jackw01/scanlight/data/big scanlight RGB combined.jpg

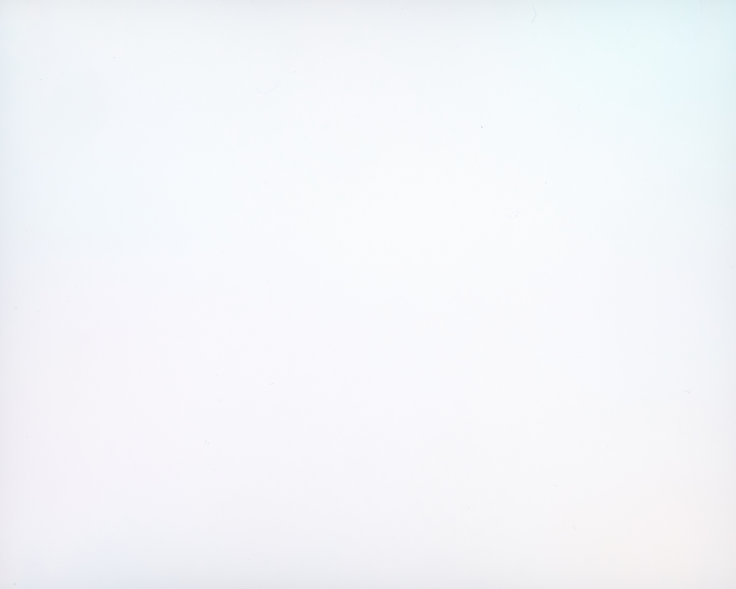
data/big scanlight RGB combined.jpg
