jackw01/scanlight/data/big scanlight white.jpg

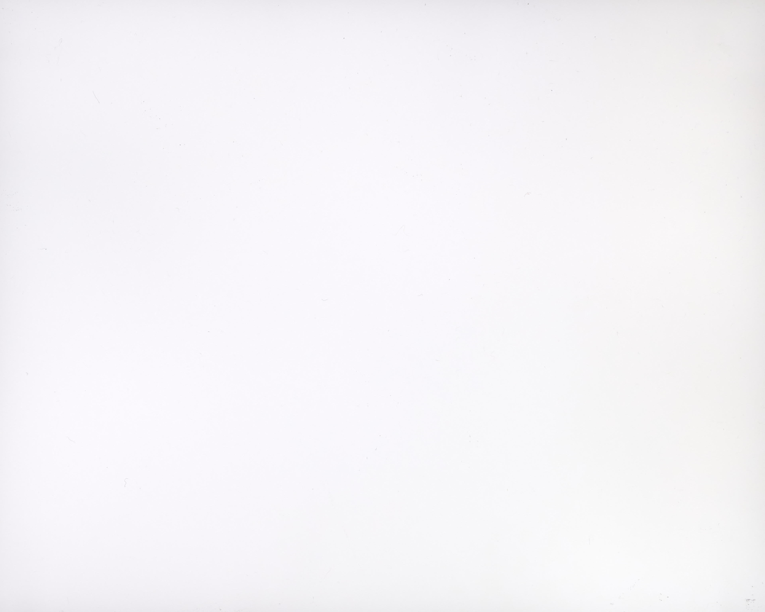
data/big scanlight white.jpg
