jackw01/scanlight/data/center of 15 inch LCD display.png

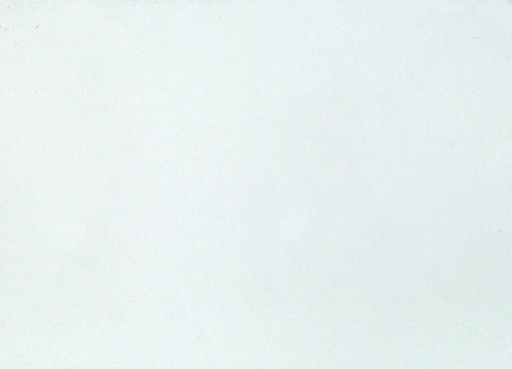
data/center of 15 inch LCD display.png
