jackw01/scanlight/data/competing white LED panel.png

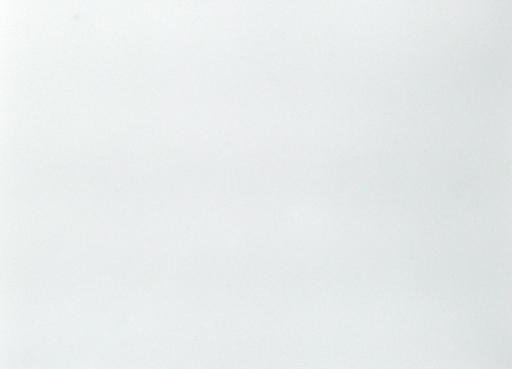
data/competing white LED panel.png
