jackw01/scanlight/data/iPhone 13 Pro.png

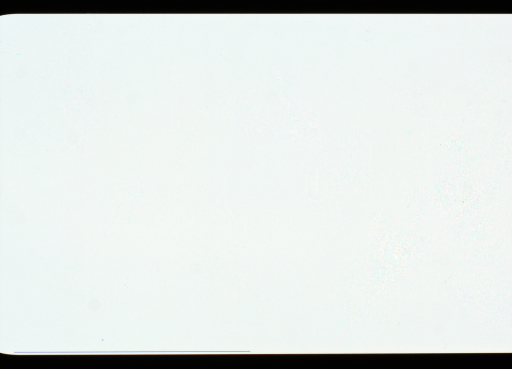
data/iPhone 13 Pro.png
