jackw01/scanlight/data/plots/luminance_plot_iPhone 13 Pro.png

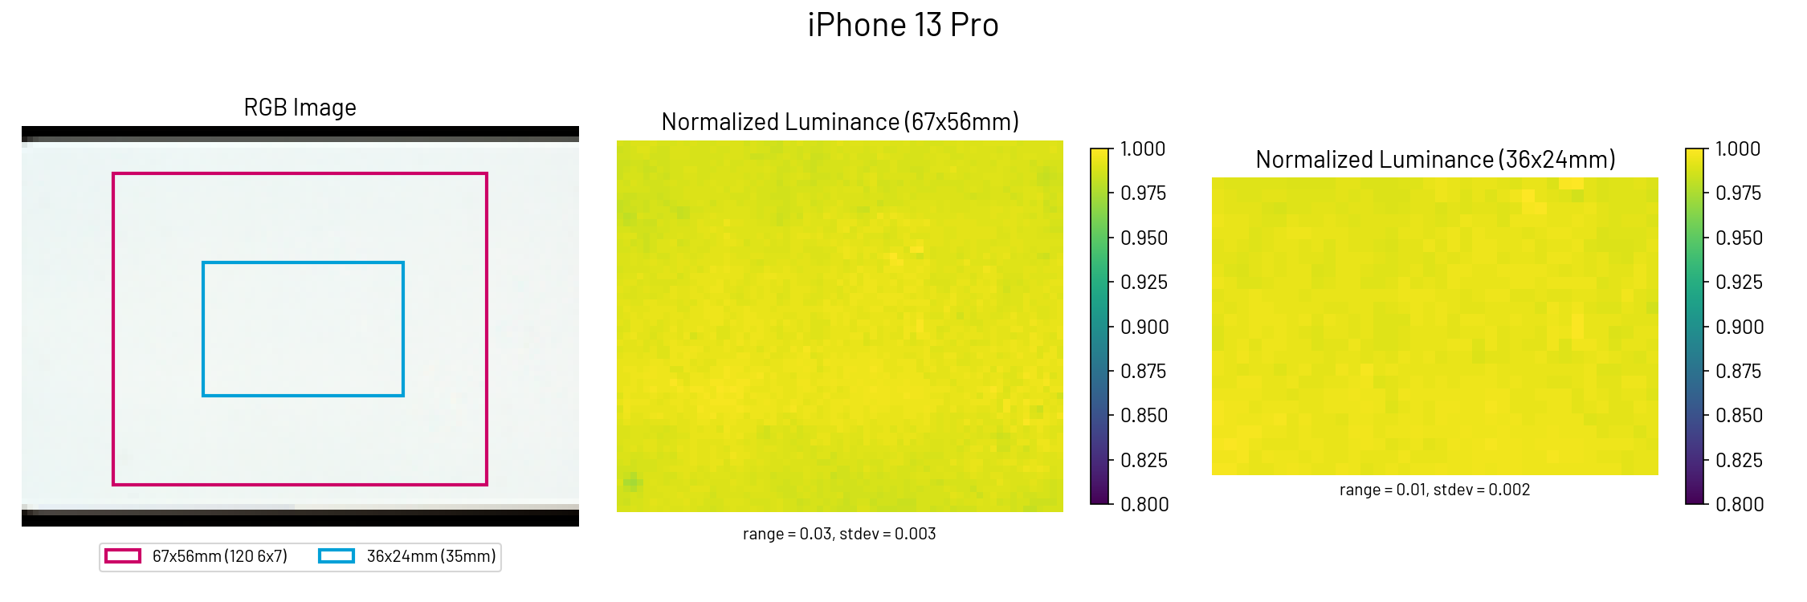
data/plots/luminance_plot_iPhone 13 Pro.png
