jackw01/scanlight/data/scanlight v1.png

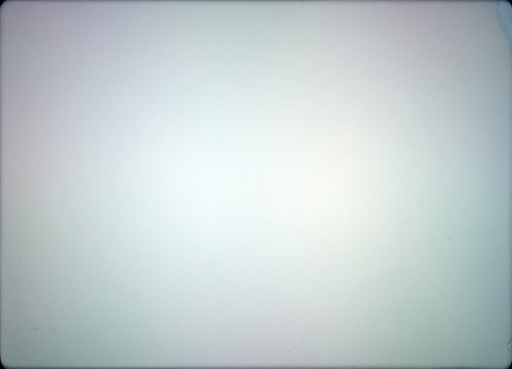
data/scanlight v1.png
