jackw01/scanlight/data/scanlight v4 RGB combined.png

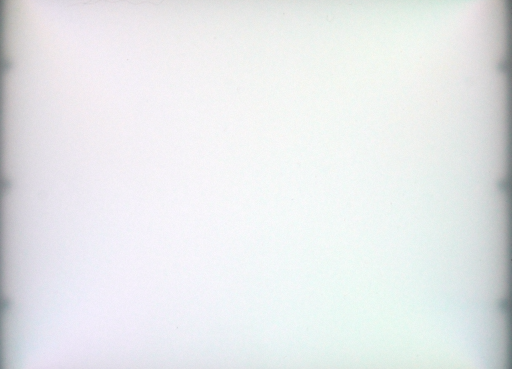
data/scanlight v4 RGB combined.png
