jackw01/scanlight/data/scanlight v4 white.png

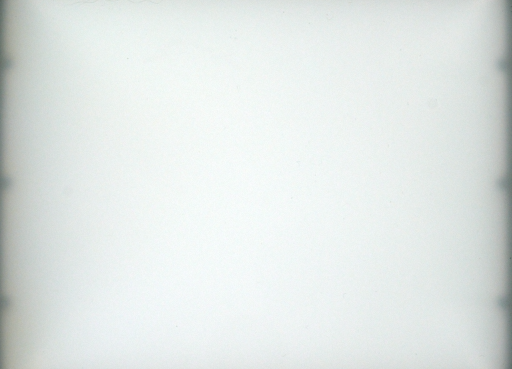
data/scanlight v4 white.png
