jackw01/scanlight/images/ac_adapter.jpg

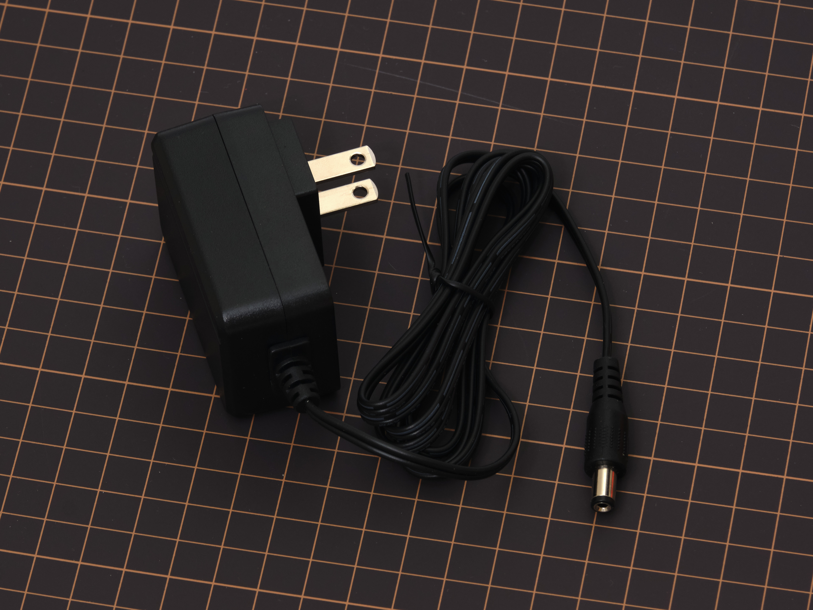
images/ac_adapter.jpg
