jackw01/scanlight/images/app.png

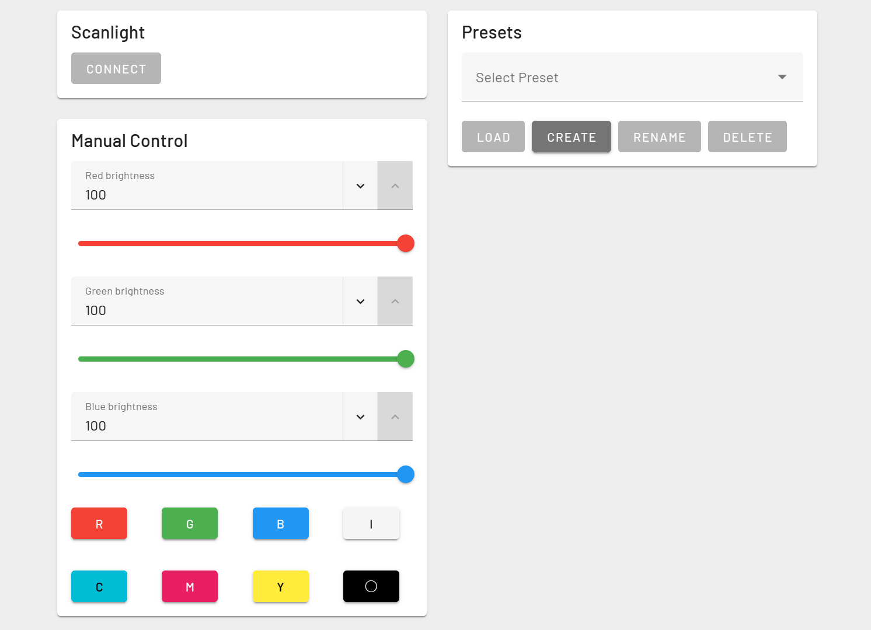
images/app.png
