jackw01/scanlight/images/big_scanlight_lit_2.jpg

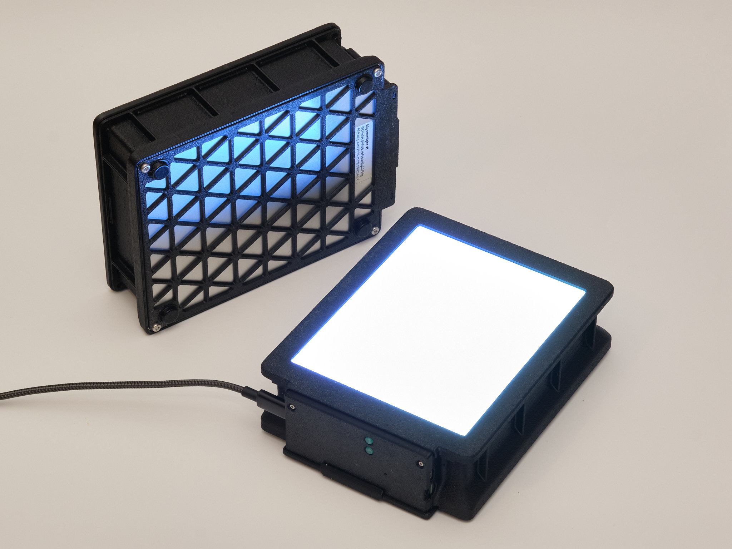
images/big_scanlight_lit_2.jpg
