jackw01/scanlight/images/big_scanlight_lit_3.jpg

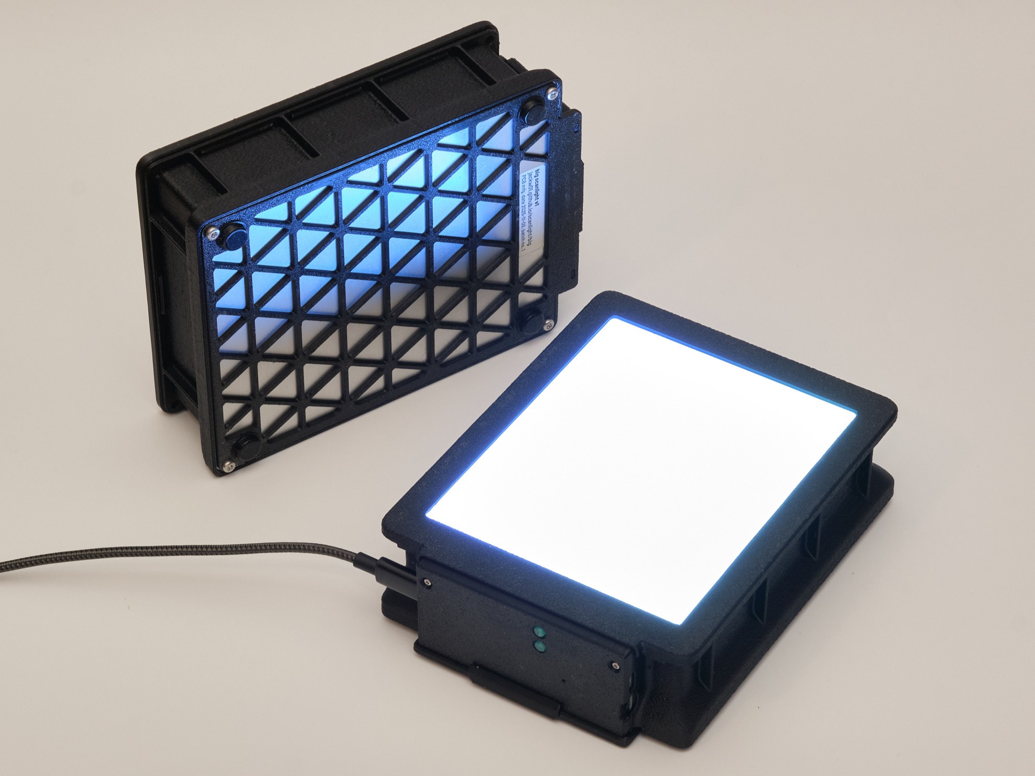
images/big_scanlight_lit_3.jpg
