jackw01/scanlight/images/big_scanlight_top.jpg

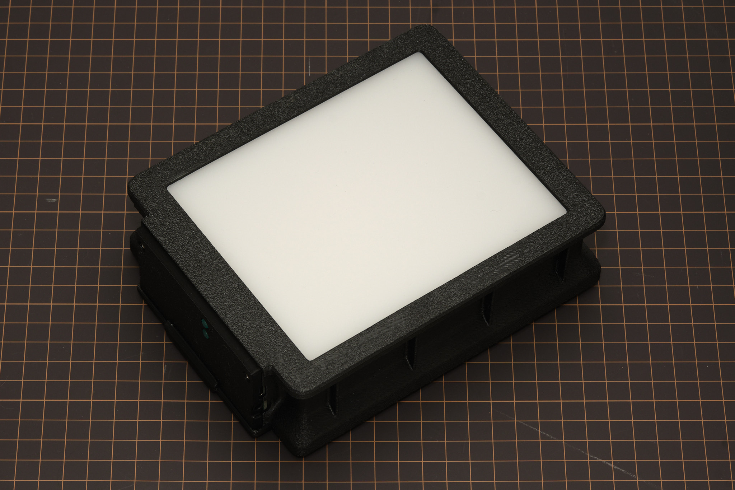
images/big_scanlight_top.jpg
