jackw01/scanlight/images/comparison3.jpg

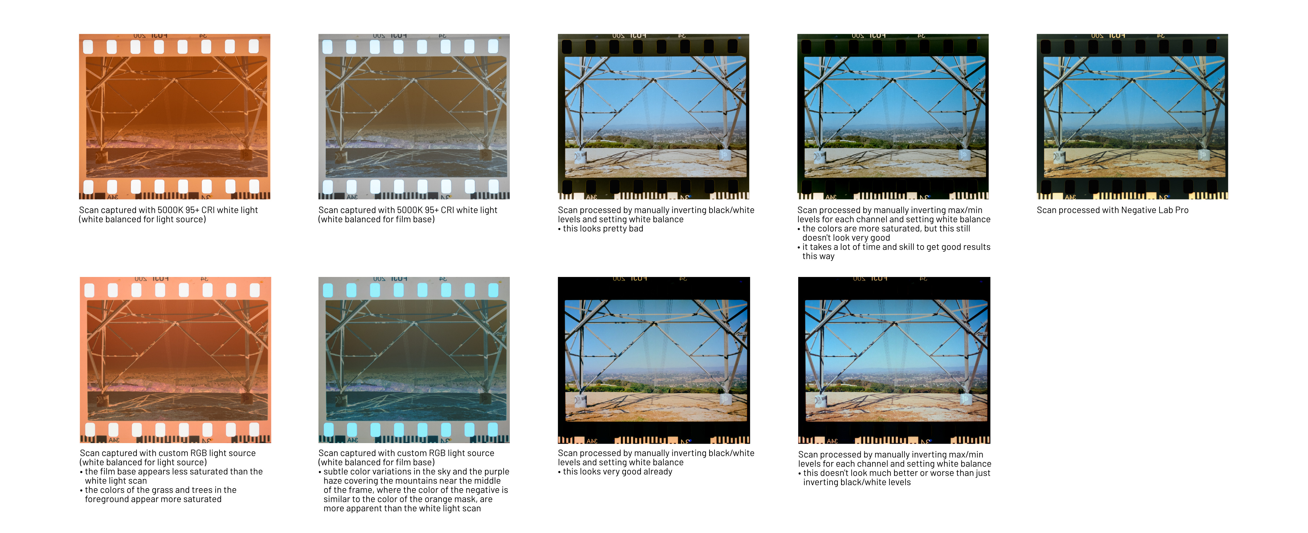
images/comparison3.jpg
