jackw01/scanlight/images/comparison.jpg

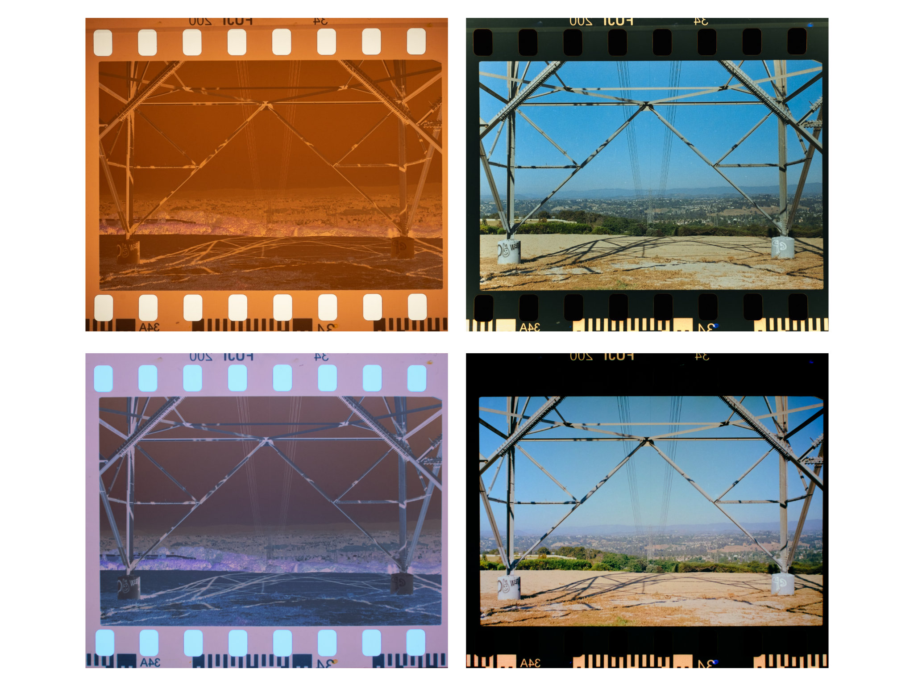
images/comparison.jpg
