jackw01/scanlight/images/diffuser_stackup.png

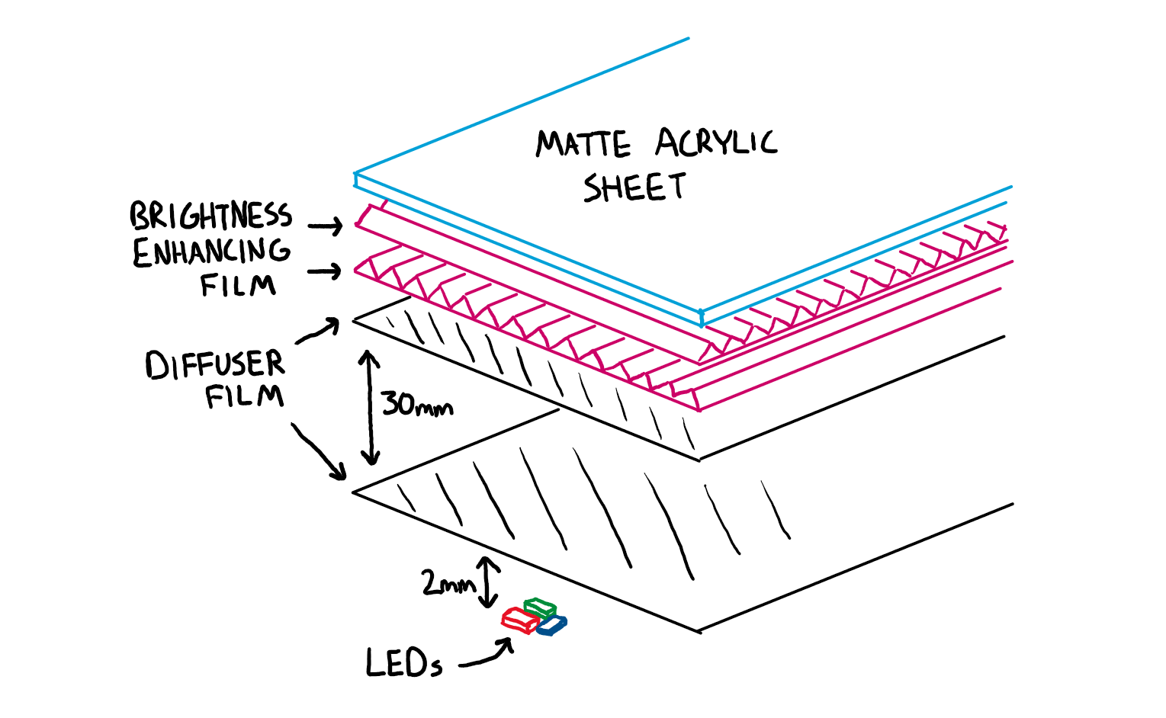
images/diffuser_stackup.png
