jackw01/scanlight/images/film_carrier_adapter.jpg

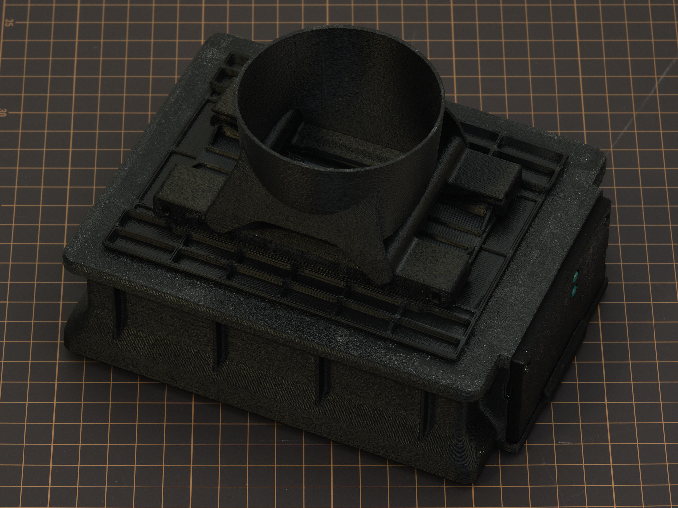
images/film_carrier_adapter.jpg
