jackw01/scanlight/images/filmcarriers_back_2.jpg

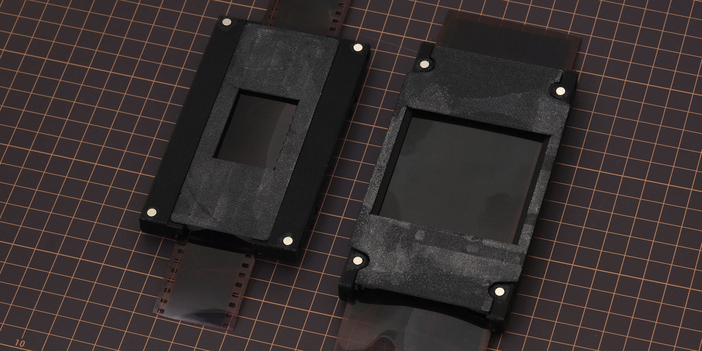
images/filmcarriers_back_2.jpg
