jackw01/scanlight/images/filmcarriers_front_2.jpg

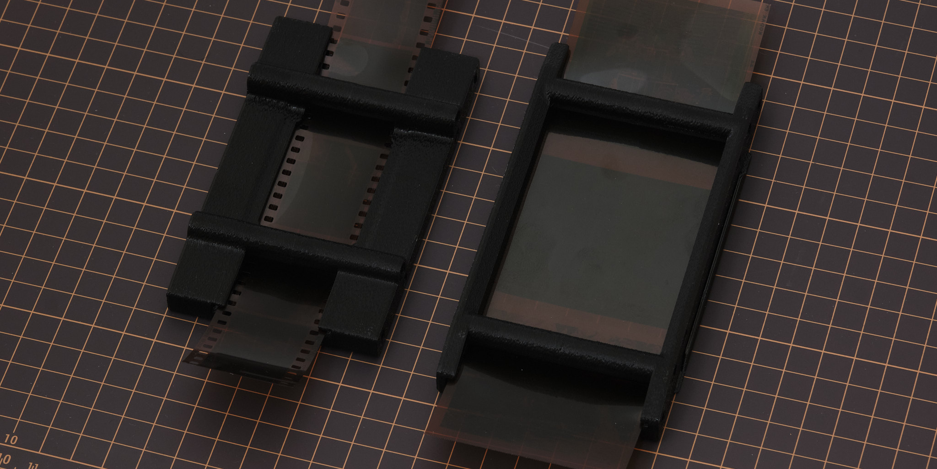
images/filmcarriers_front_2.jpg
