jackw01/scanlight/images/light_with_film_v2_2.jpg

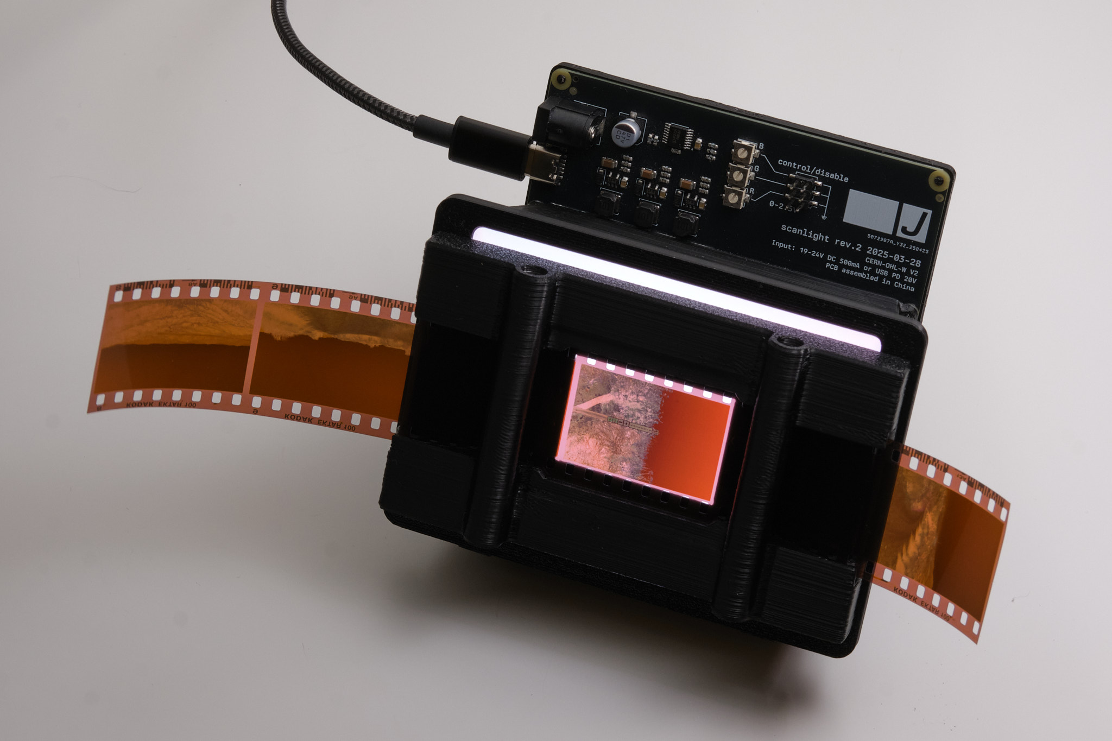
images/light_with_film_v2_2.jpg
