jackw01/scanlight/images/pcb.jpg

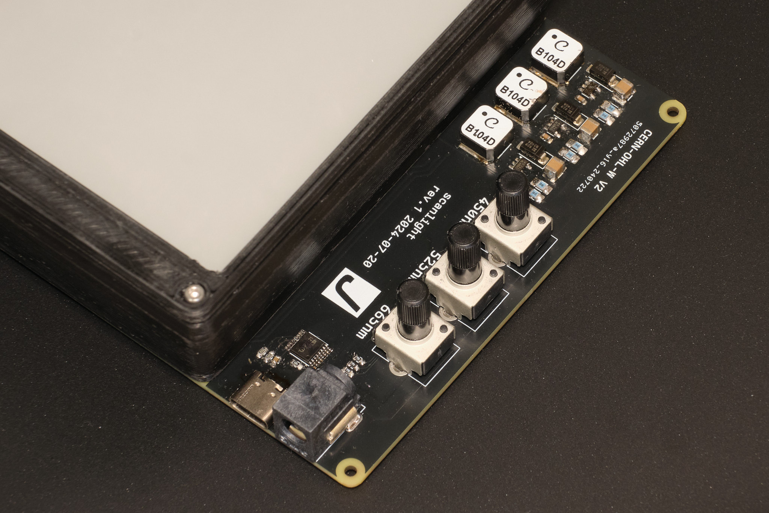
images/pcb.jpg
