jackw01/scanlight/images/pcb_cad.png

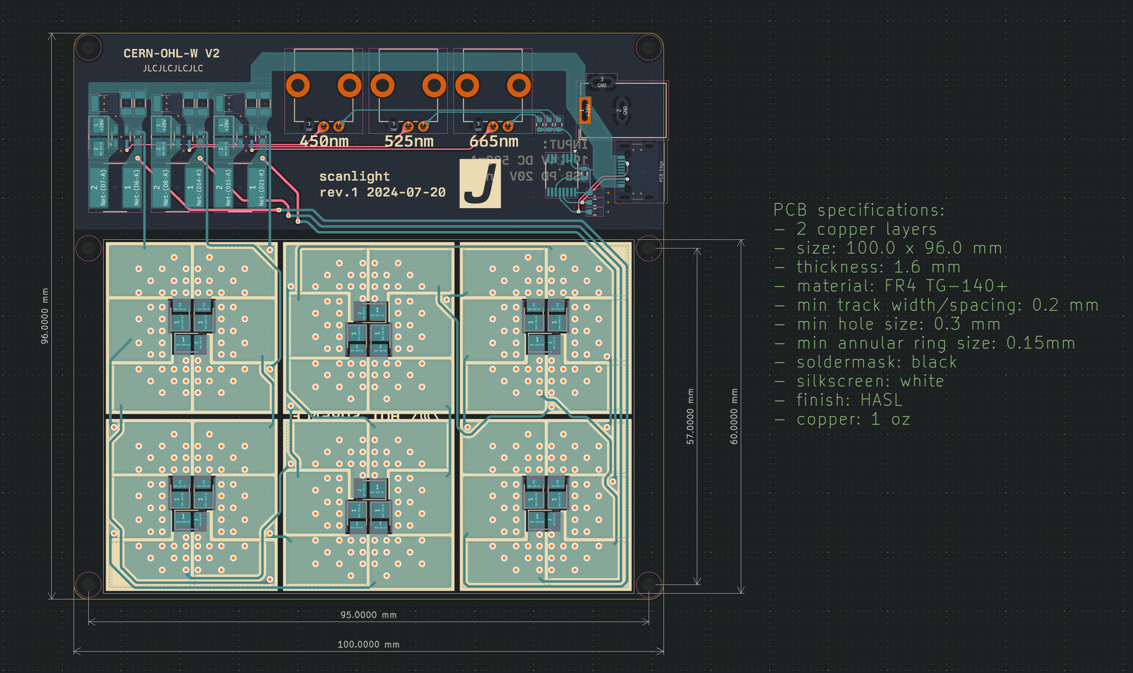
images/pcb_cad.png
