jackw01/scanlight/images/pcb_cad_r2.png

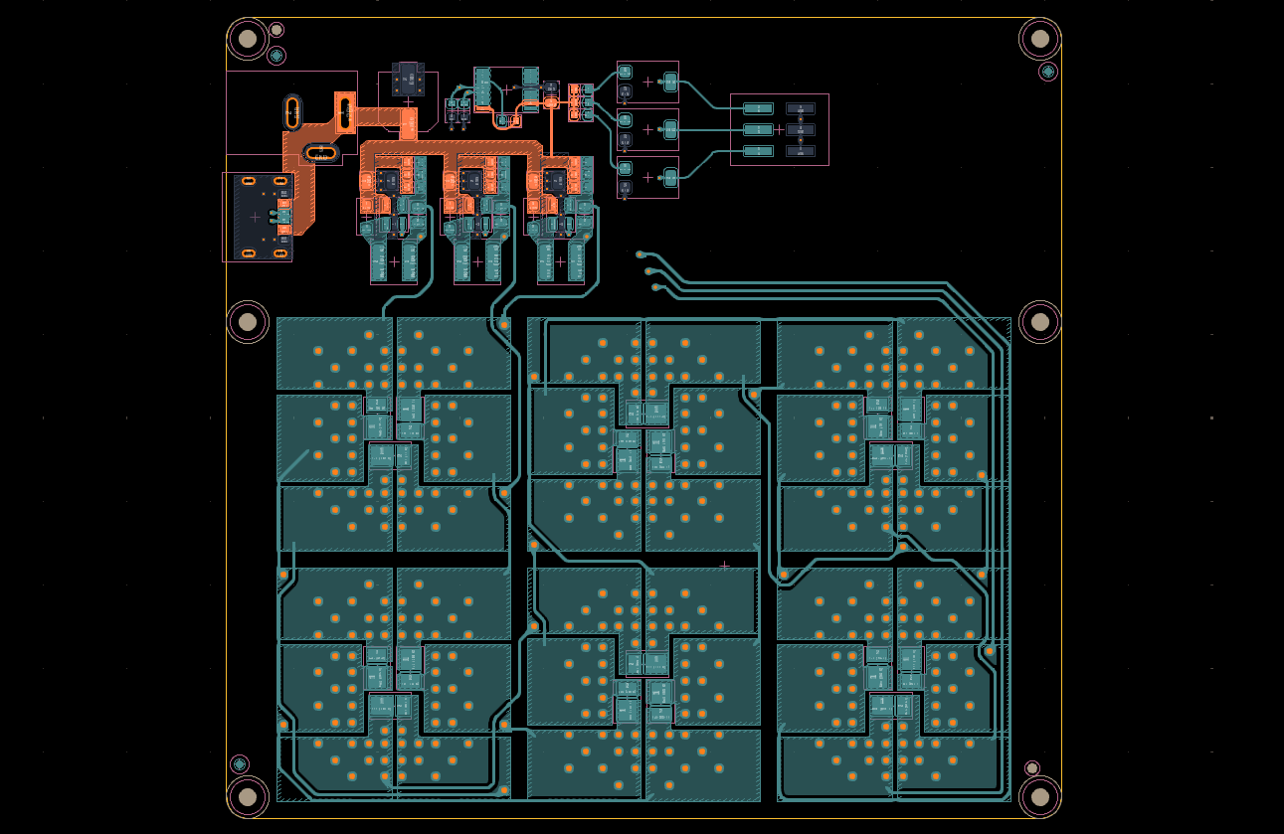
images/pcb_cad_r2.png
