jackw01/scanlight/images/pcb_r2.png

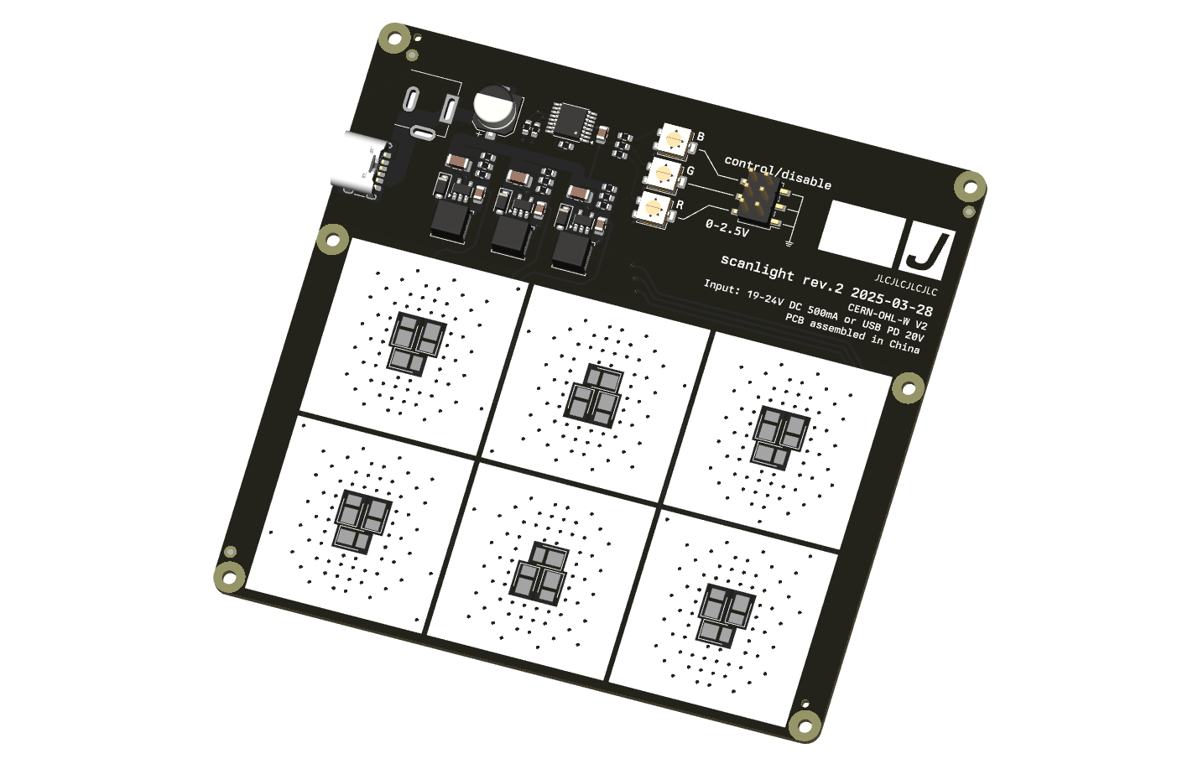
images/pcb_r2.png
