jackw01/scanlight/images/scan_comparison_aerocolor_1.jpg

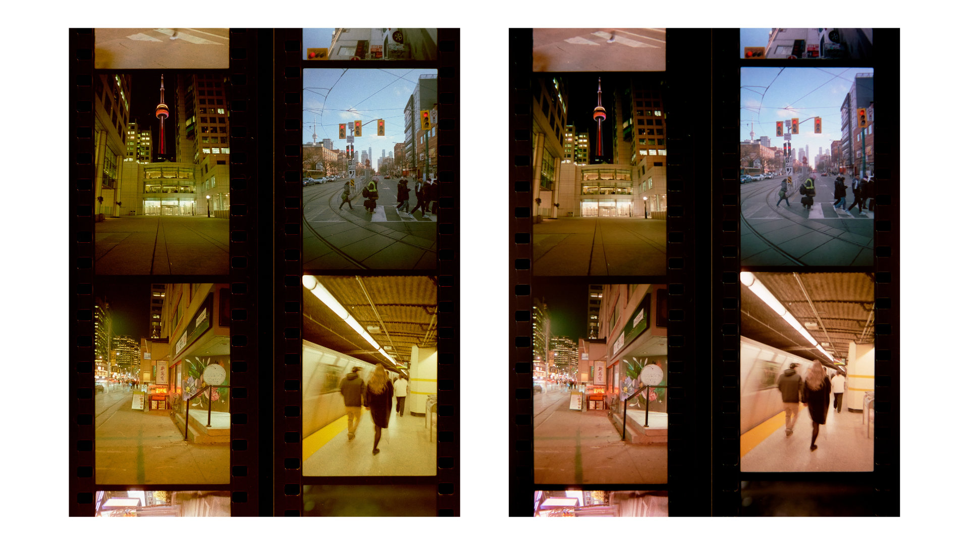
images/scan_comparison_aerocolor_1.jpg
