jackw01/scanlight/images/scan_comparison_ektar_3.jpg

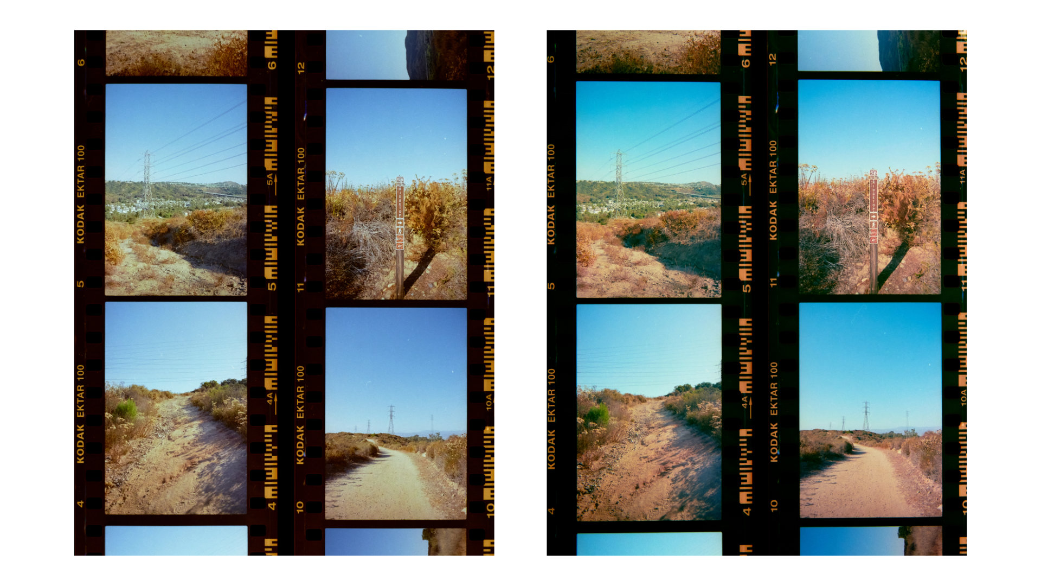
images/scan_comparison_ektar_3.jpg
