jackw01/scanlight/images/scan_comparison_fuji200_1.jpg

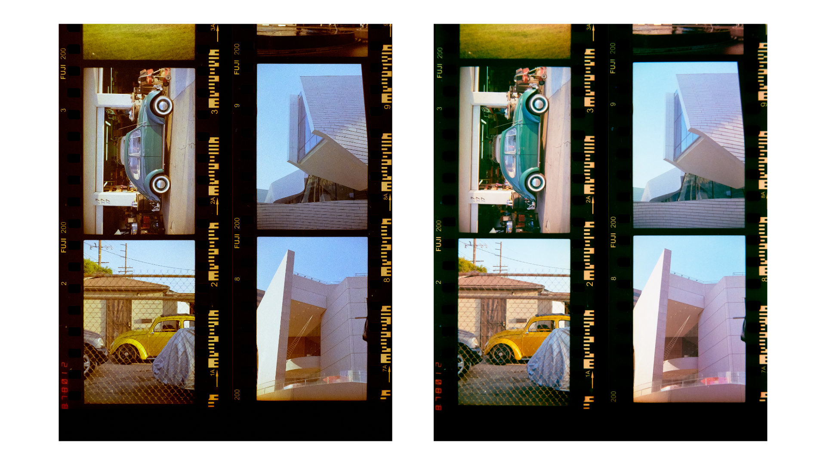
images/scan_comparison_fuji200_1.jpg
