jackw01/scanlight/images/scan_comparison_fuji200_2.jpg

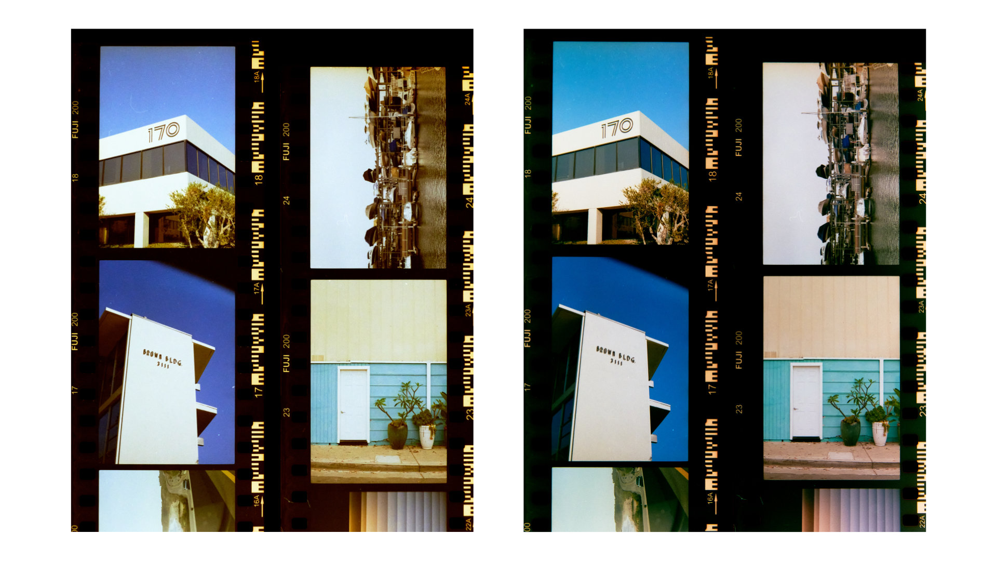
images/scan_comparison_fuji200_2.jpg
