jackw01/scanlight/images/scanlight_v2_back.jpg

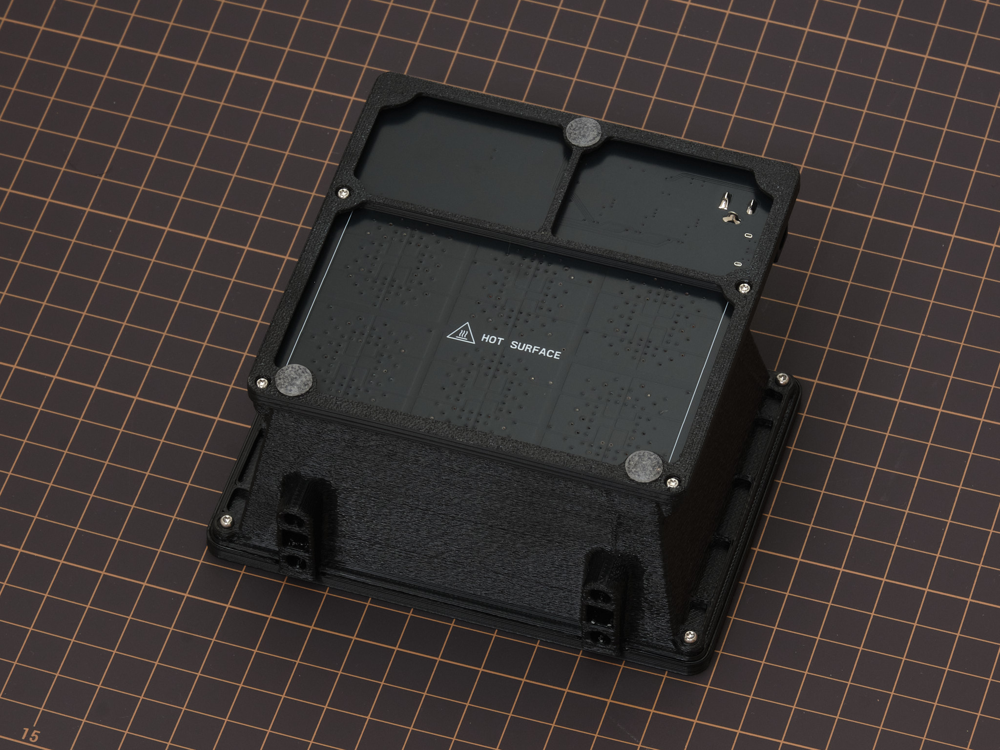
images/scanlight_v2_back.jpg
