jackw01/scanlight/images/scanlight_v2_cad.png

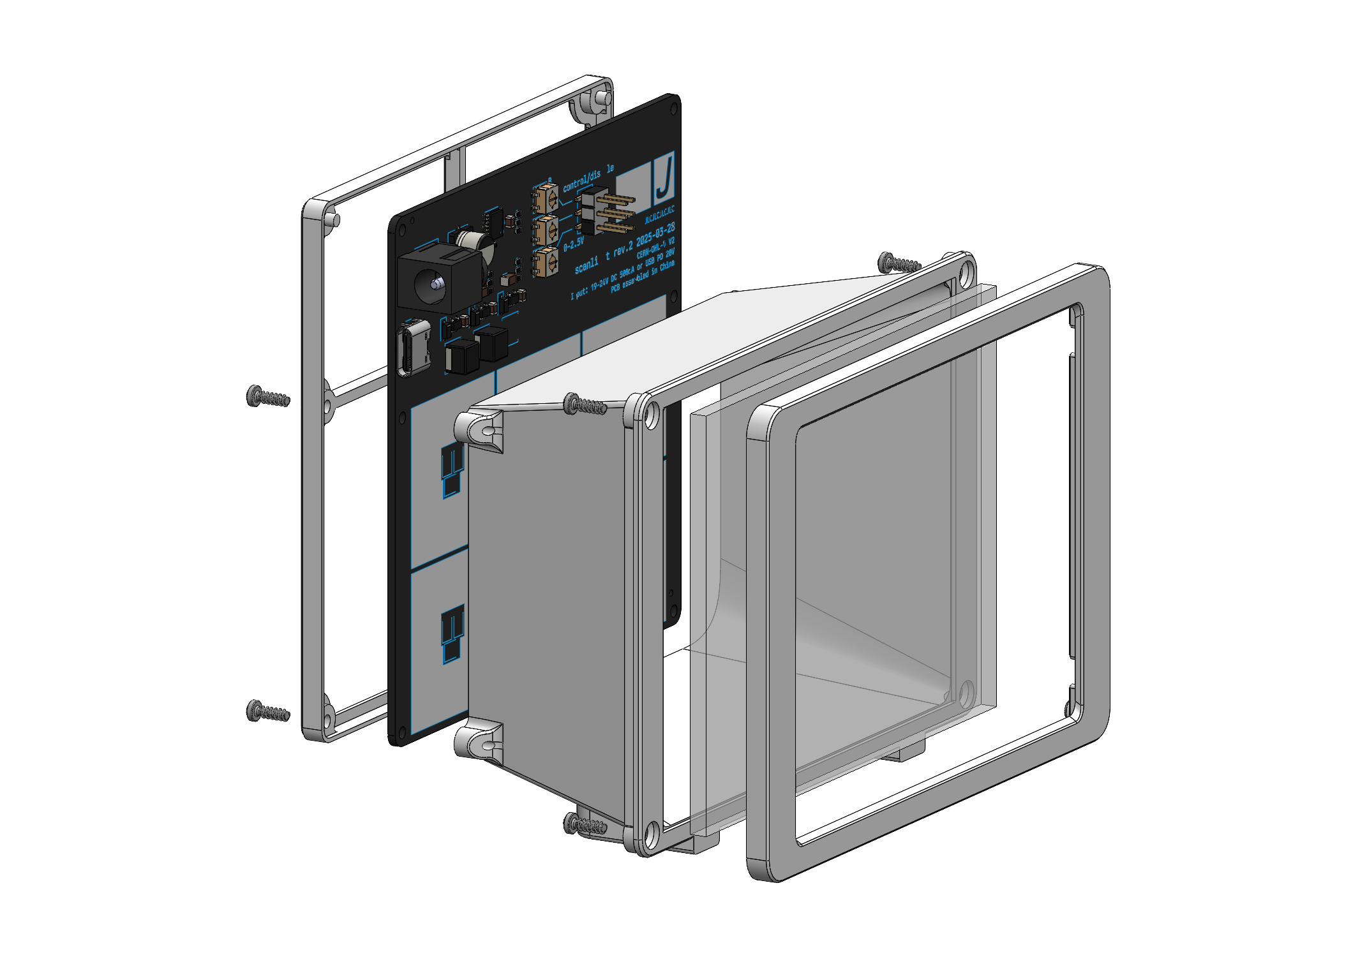
images/scanlight_v2_cad.png
