jackw01/scanlight/images/scanlight_v4_bottom.jpg

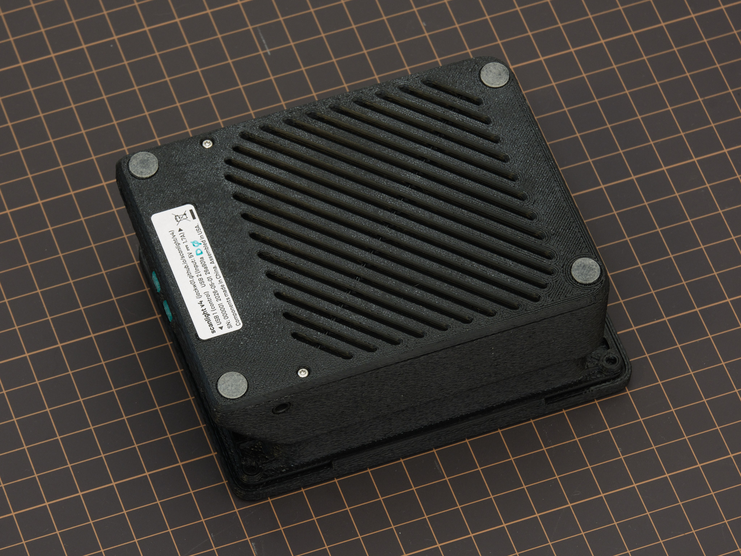
images/scanlight_v4_bottom.jpg
