jackw01/scanlight/images/scanlight_v4_dimension_drawing.png

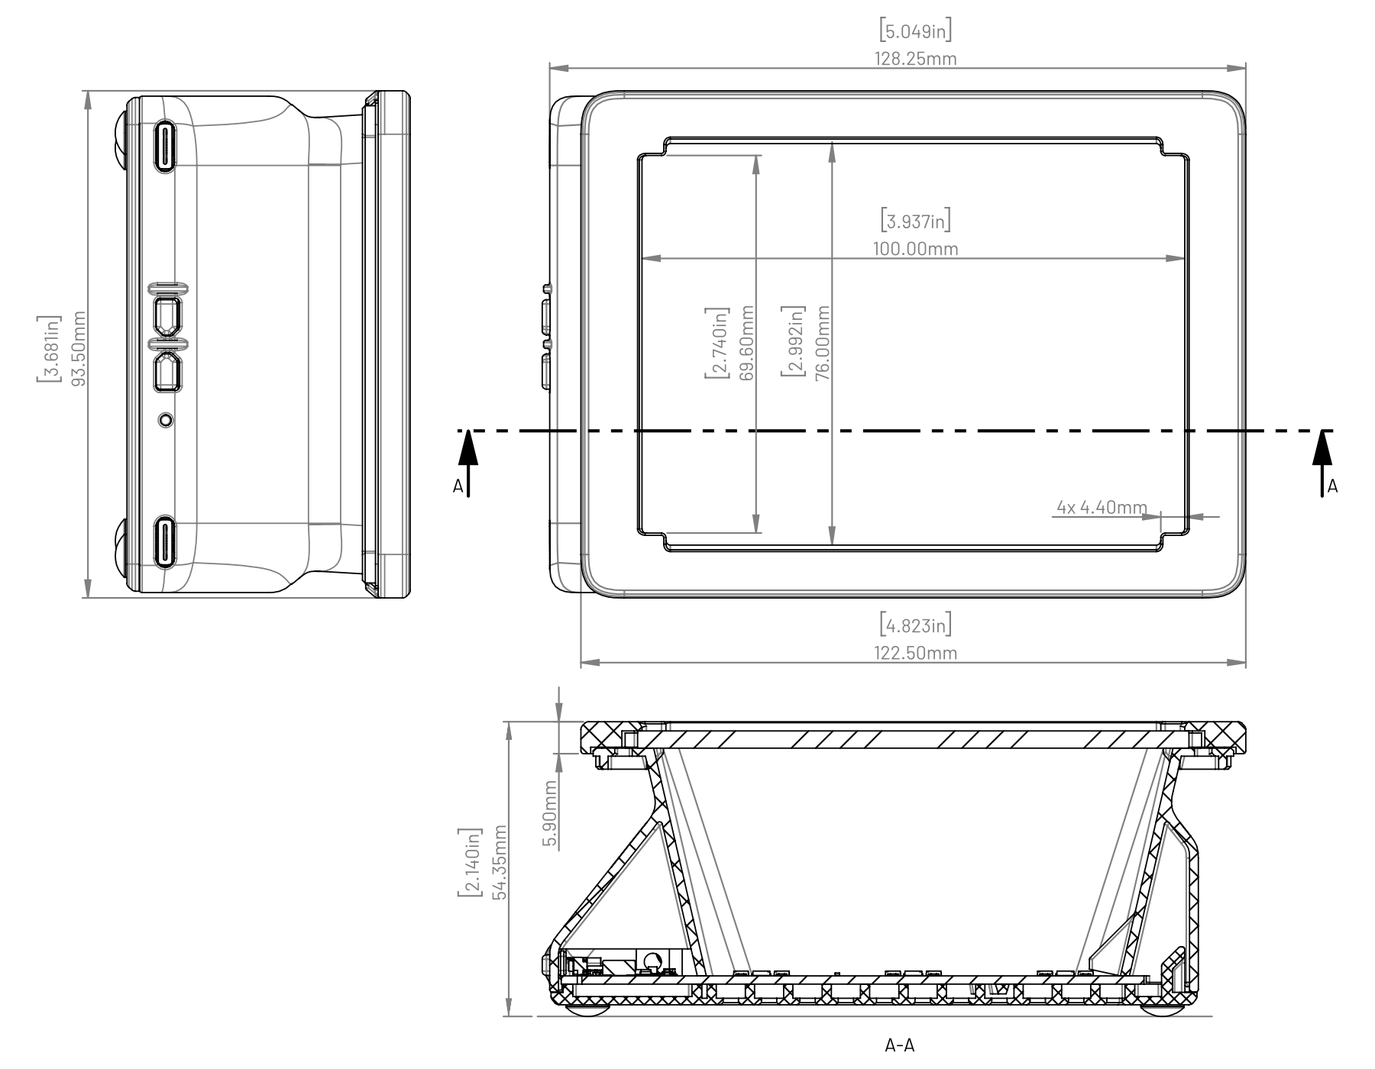
images/scanlight_v4_dimension_drawing.png
