jackw01/scanlight/images/scanlight_v4_lit_2.jpg

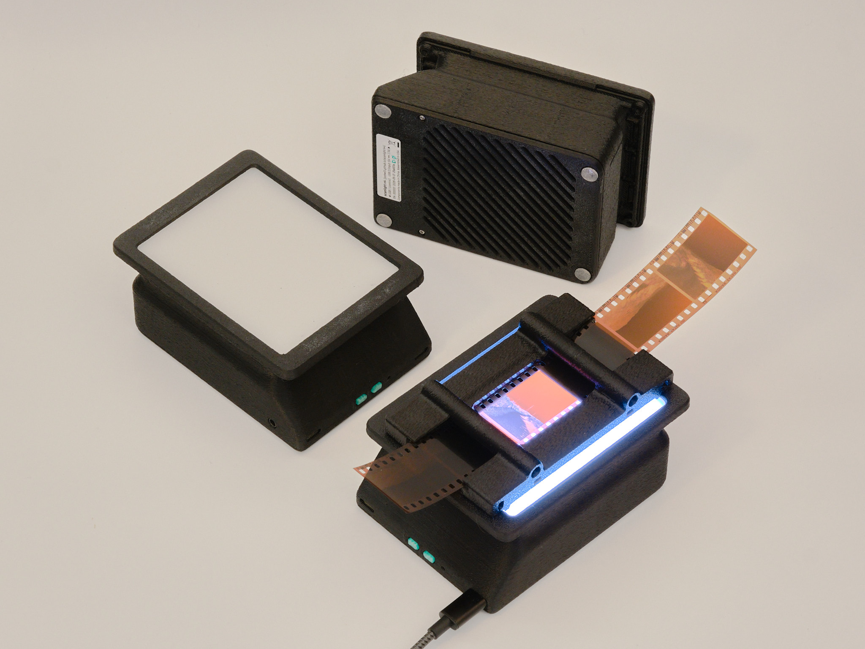
images/scanlight_v4_lit_2.jpg
