jackw01/scanlight/images/webapp.png

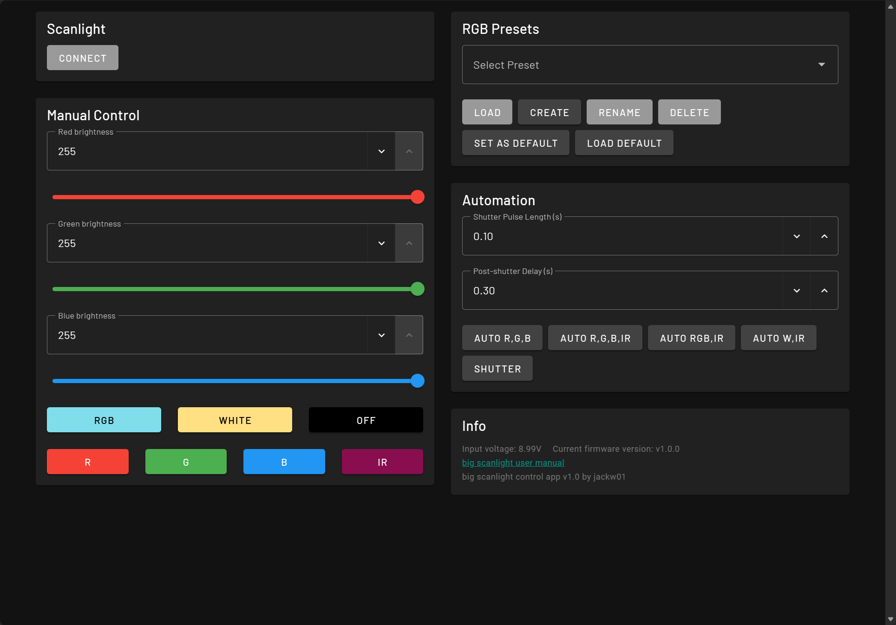
images/webapp.png
