jackw01/scanlight/3d/scanlight v4/26a110b tonecarrier compatibility plate.step

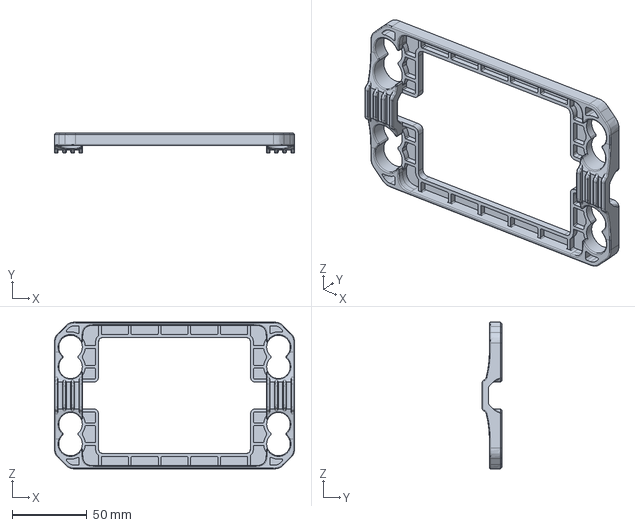
[picture p106: CAD file, 2026-06-06]
3d/scanlight v4/26a110b tonecarrier compatibility plate.step
161.0 x 13.5 x 98.4 mm
