jackw01/scanlight/3d/big scanlight v1/25d107 button.step

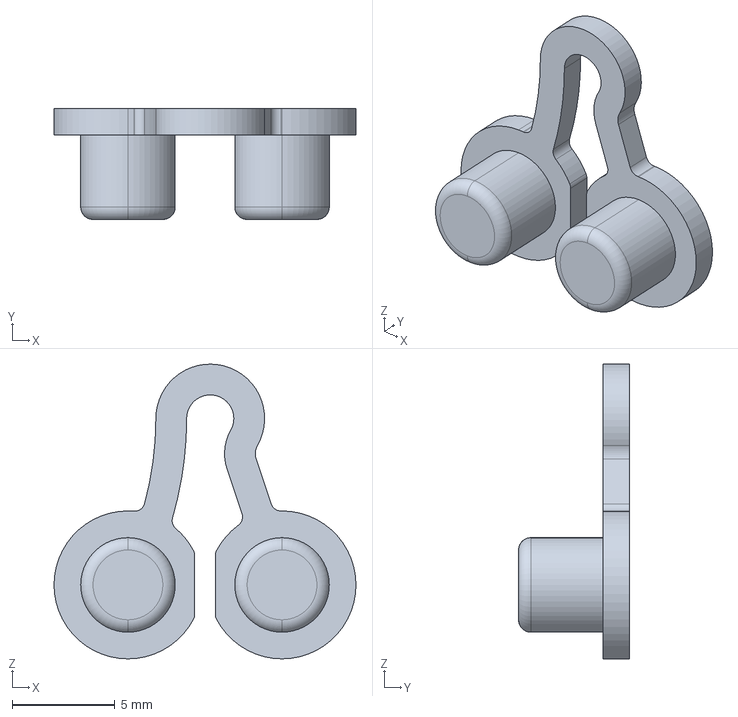
[picture p107: CAD file, 2026-09-24]
3d/big scanlight v1/25d107 button.step
14.7 x 5.40 x 14.3 mm
