jackw01/scanlight/3d/film carriers v1.1/25c014 120 68 mask.step

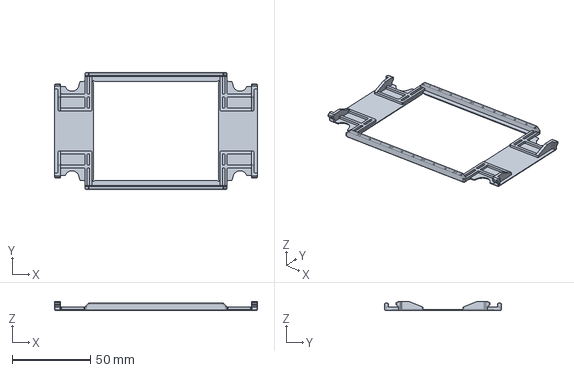
[picture p108: CAD file, 2026-05-09]
3d/film carriers v1.1/25c014 120 68 mask.step
130.0 x 75.0 x 5.80 mm
