jackw01/scanlight/3d/horizontal/25c036 camera clamp cam.step

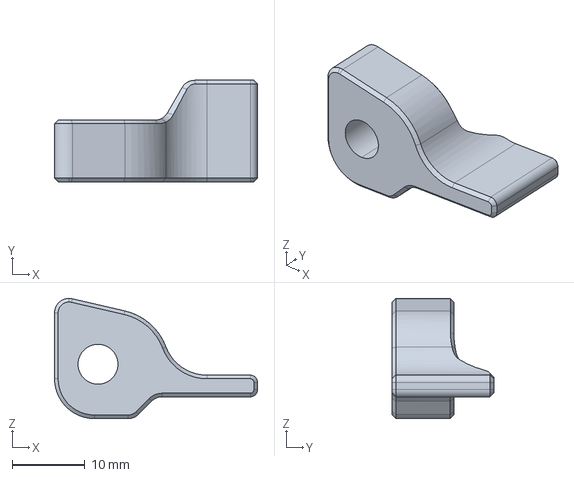
[picture p109: CAD file, 2025-08-15]
3d/horizontal/25c036 camera clamp cam.step
28.0 x 14.0 x 16.6 mm
