jackw01/scanlight/3d/light source v3/25c-p003b diffuser bezel.step

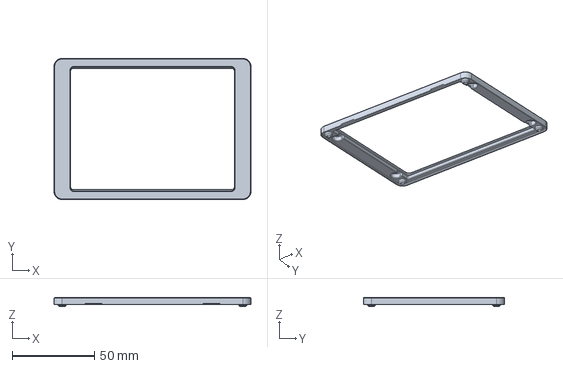
[picture p110: CAD file, 2025-08-02]
3d/light source v3/25c-p003b diffuser bezel.step
120.0 x 86.0 x 5.60 mm
