jackw01/scanlight/3d/scanlight v4/26a005 pcb cover.step

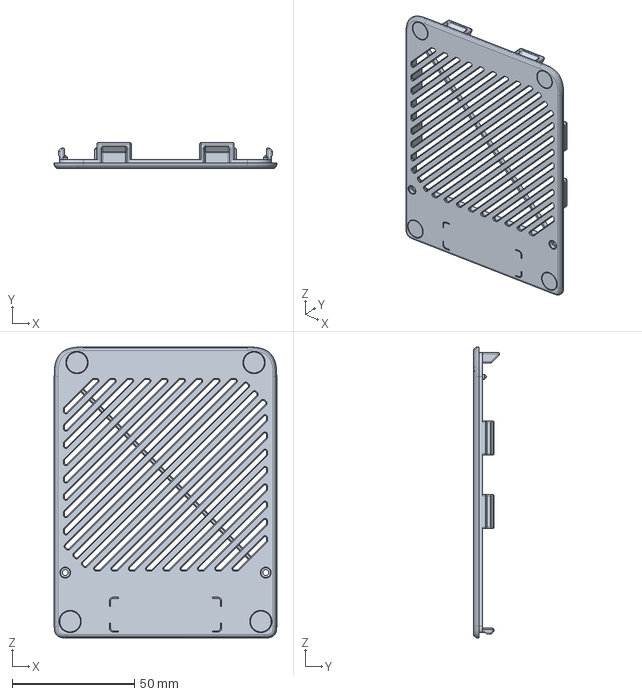
[picture p111: CAD file, 2026-05-09]
3d/scanlight v4/26a005 pcb cover.step
91.0 x 10.7 x 119.0 mm
