jackw01/scanlight/3d/big scanlight v1/25d104 backplate.step

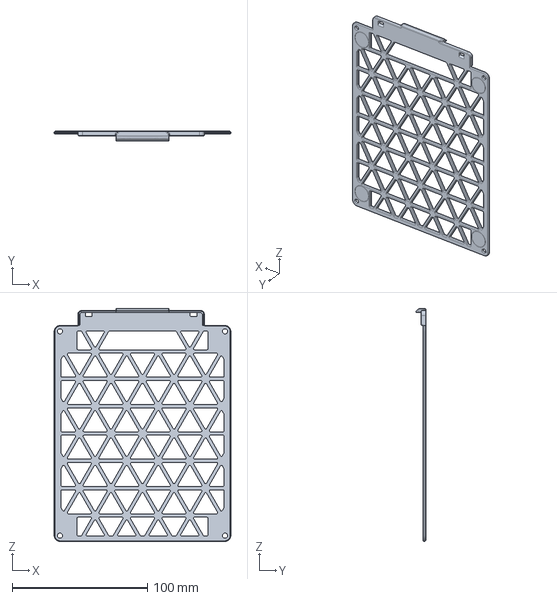
[picture p112: CAD file, 2026-09-24]
3d/big scanlight v1/25d104 backplate.step
130.7 x 7.10 x 172.2 mm
