jackw01/scanlight/3d/film carriers v1.1/25c020 35mm half frame mask.step

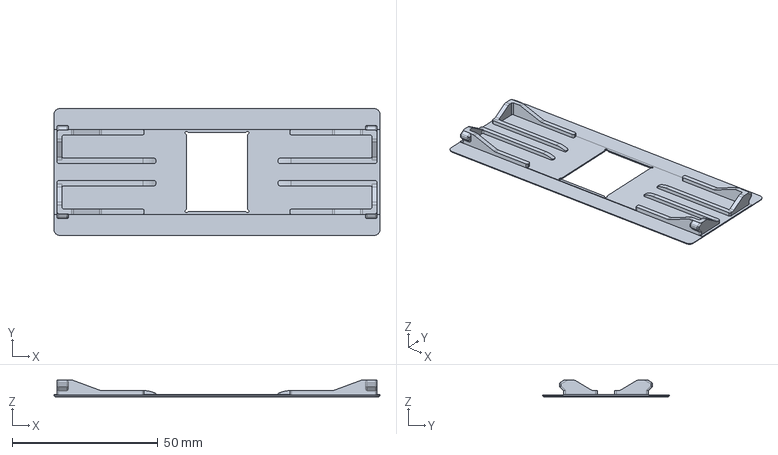
[picture p113: CAD file, 2026-05-09]
3d/film carriers v1.1/25c020 35mm half frame mask.step
112.0 x 43.6 x 5.80 mm
