jackw01/scanlight/3d/horizontal/25c037 M3 spacer 1mm.step

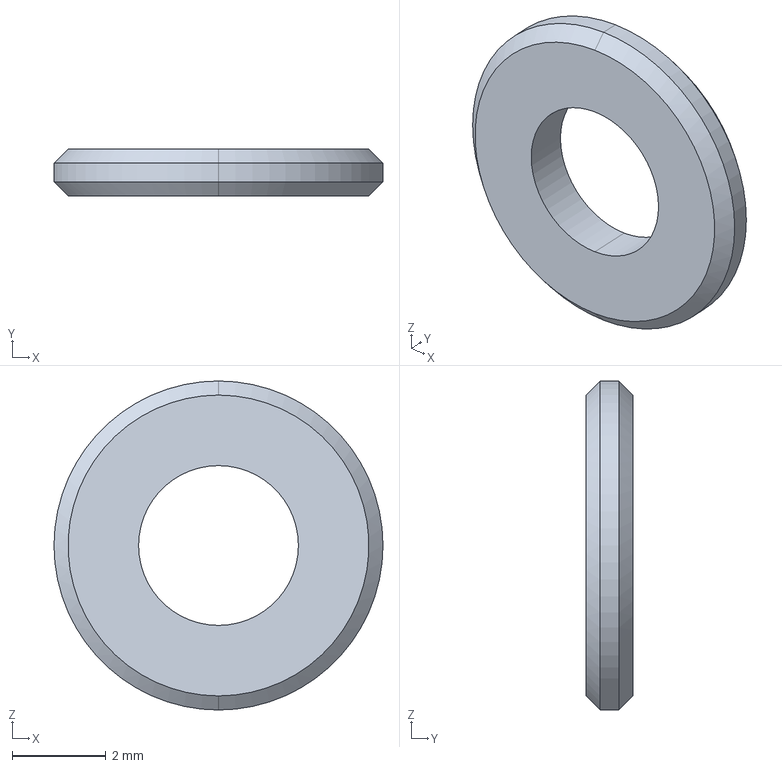
[picture p114: CAD file, 2025-08-15]
3d/horizontal/25c037 M3 spacer 1mm.step
7.00 x 1.00 x 7.00 mm
