jackw01/scanlight/3d/light source v3/25c-p001f reflector box housing.step

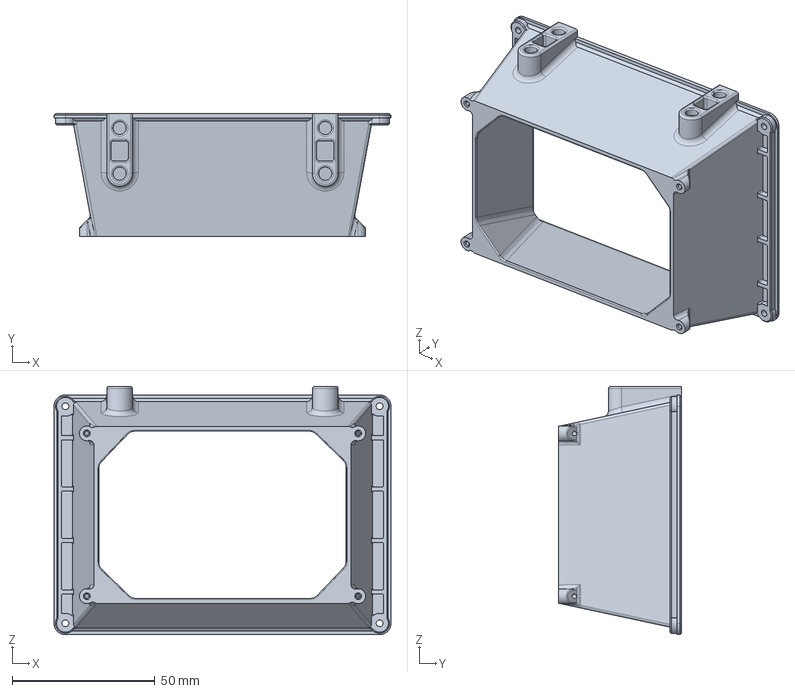
[picture p115: CAD file, 2025-08-02]
3d/light source v3/25c-p001f reflector box housing.step
118.0 x 42.9 x 87.0 mm
