jackw01/scanlight/3d/scanlight v4/26a003b diffuser bezel.step

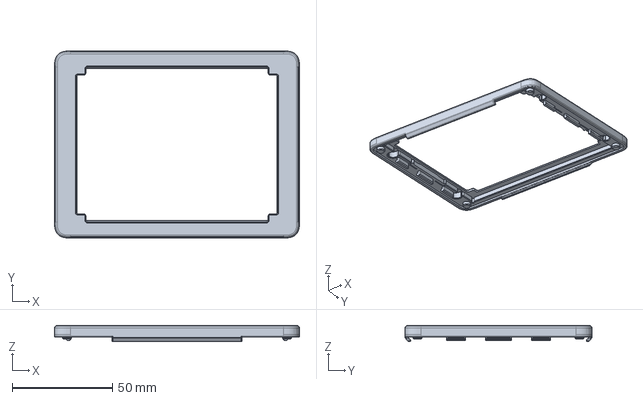
[picture p116: CAD file, 2026-05-09]
3d/scanlight v4/26a003b diffuser bezel.step
122.5 x 93.5 x 8.20 mm
