jackw01/scanlight/3d/big scanlight v1/25d114b lobster compatibility plate.step

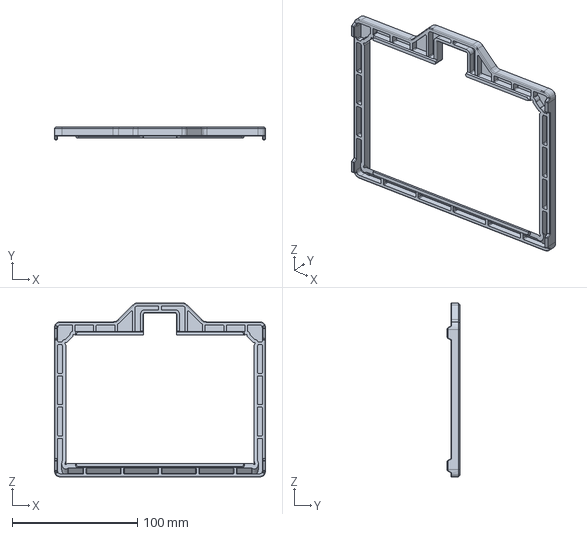
[picture p117: CAD file, 2026-09-15]
3d/big scanlight v1/25d114b lobster compatibility plate.step
168.6 x 10.0 x 139.0 mm
