jackw01/scanlight/3d/film carriers v1.1/25c012 35mm film carrier half.step

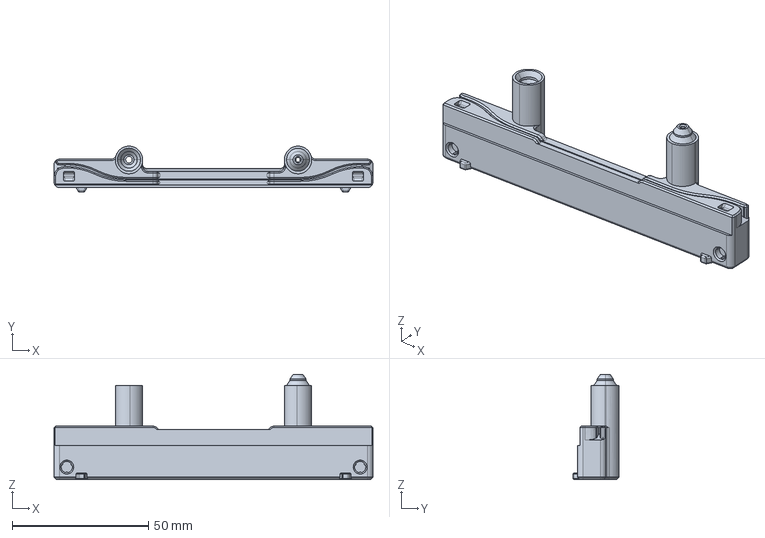
[picture p118: CAD file, 2026-05-09]
3d/film carriers v1.1/25c012 35mm film carrier half.step
117.0 x 16.8 x 38.6 mm
