jackw01/scanlight/3d/scanlight v4/26a111 valoi 360 advancer compatibility plate.step

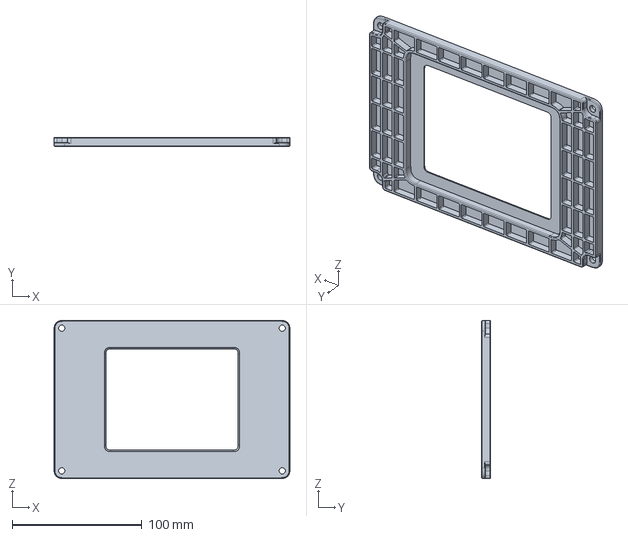
[picture p119: CAD file, 2026-05-09]
3d/scanlight v4/26a111 valoi 360 advancer compatibility plate.step
182.0 x 7.00 x 122.0 mm
