jackw01/scanlight/3d/big scanlight v1/25d115 efh compatibility plate.step

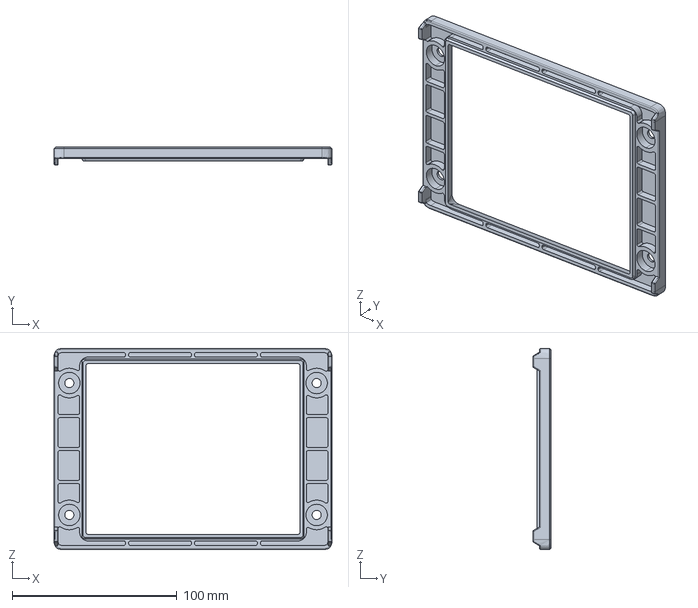
[picture p120: CAD file, 2026-09-15]
3d/big scanlight v1/25d115 efh compatibility plate.step
168.6 x 11.0 x 122.0 mm
