jackw01/scanlight/3d/scanlight v4/26a004 button.step

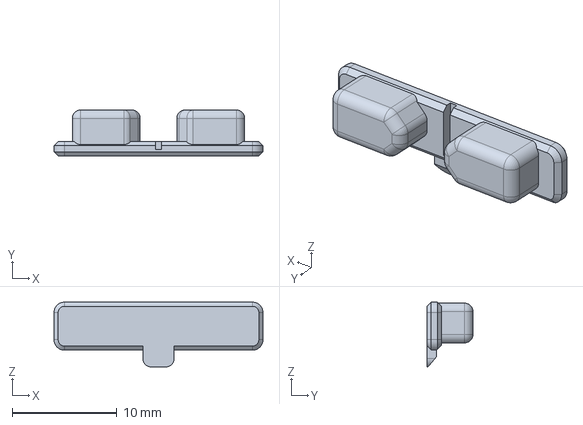
[picture p122: CAD file, 2026-05-09]
3d/scanlight v4/26a004 button.step
20.0 x 4.40 x 6.20 mm
