jackw01/scanlight/3d/big scanlight v1/25d108b film carrier compatibility plate.step

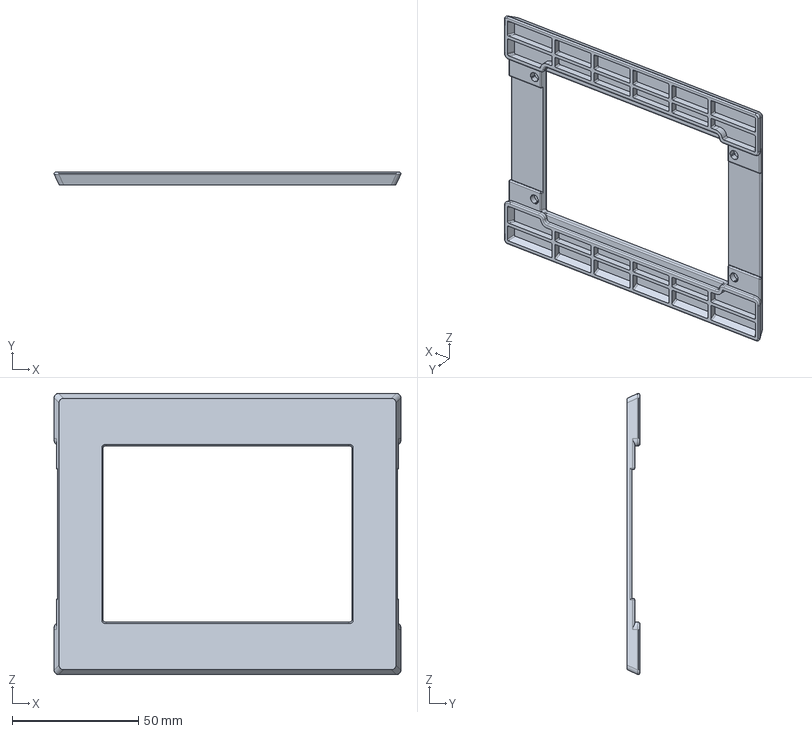
[picture p123: CAD file, 2026-05-09]
3d/big scanlight v1/25d108b film carrier compatibility plate.step
137.5 x 5.00 x 111.5 mm
