jackw01/scanlight/3d/big scanlight v1/25d112 valoi easy120 baseplate.step

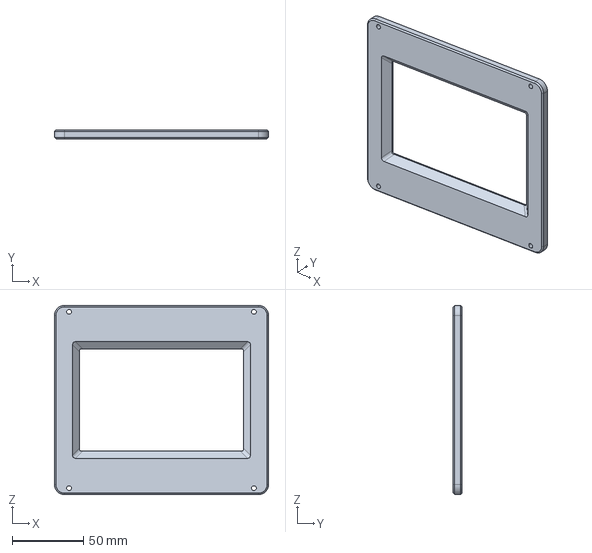
[picture p125: CAD file, 2026-05-08]
3d/big scanlight v1/25d112 valoi easy120 baseplate.step
150.5 x 6.00 x 133.0 mm
