jackw01/scanlight/3d/film carriers v1.1/25c013 120 film carrier half.step

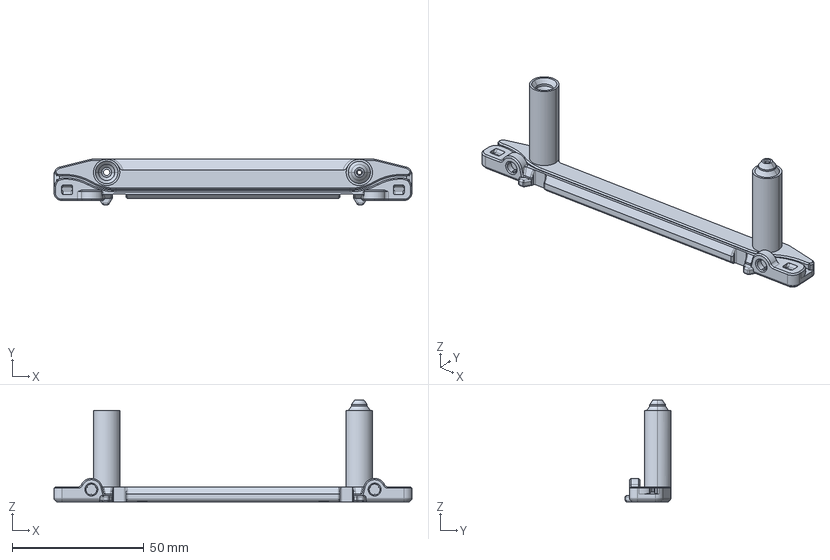
[picture p126: CAD file, 2026-05-09]
3d/film carriers v1.1/25c013 120 film carrier half.step
136.0 x 17.3 x 38.7 mm
