jackw01/scanlight/3d/big scanlight v1/25d110 tonecarrier compatibility plate.step

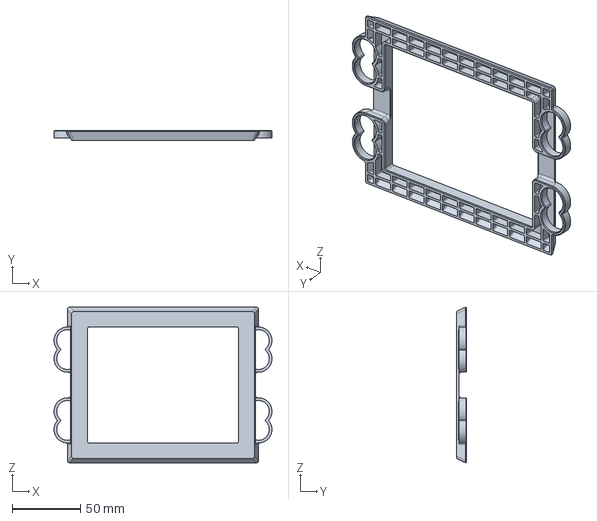
[picture p128: CAD file, 2026-05-08]
3d/big scanlight v1/25d110 tonecarrier compatibility plate.step
159.3 x 7.50 x 113.8 mm
