jackw01/scanlight/3d/big scanlight v1/25d113 valoi easy120 mounting block.step

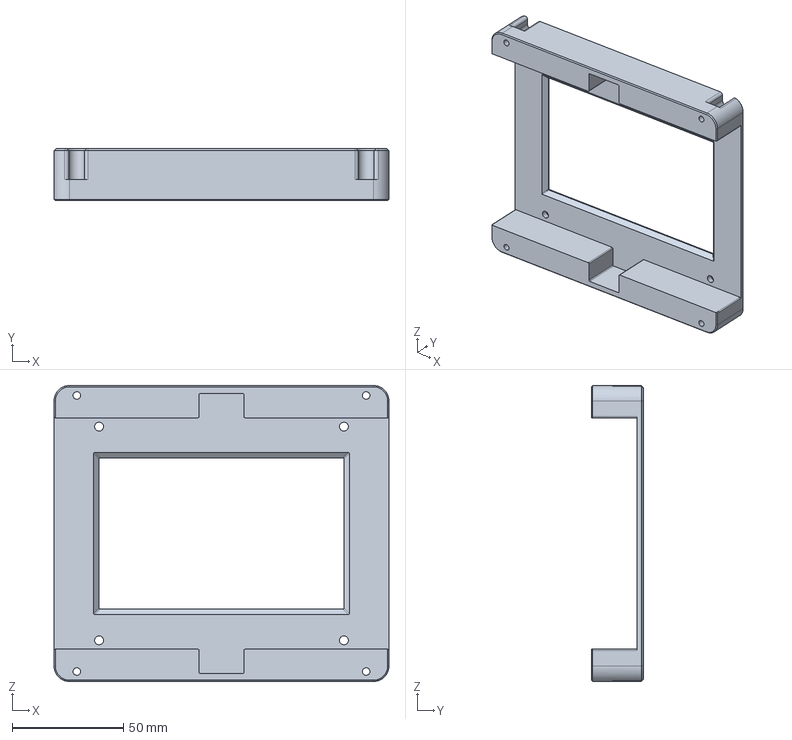
[picture p129: CAD file, 2026-05-08]
3d/big scanlight v1/25d113 valoi easy120 mounting block.step
150.5 x 23.5 x 133.0 mm
