jackw01/scanlight/3d/big scanlight v1/25d111 valoi 360 advancer compatibility plate.step

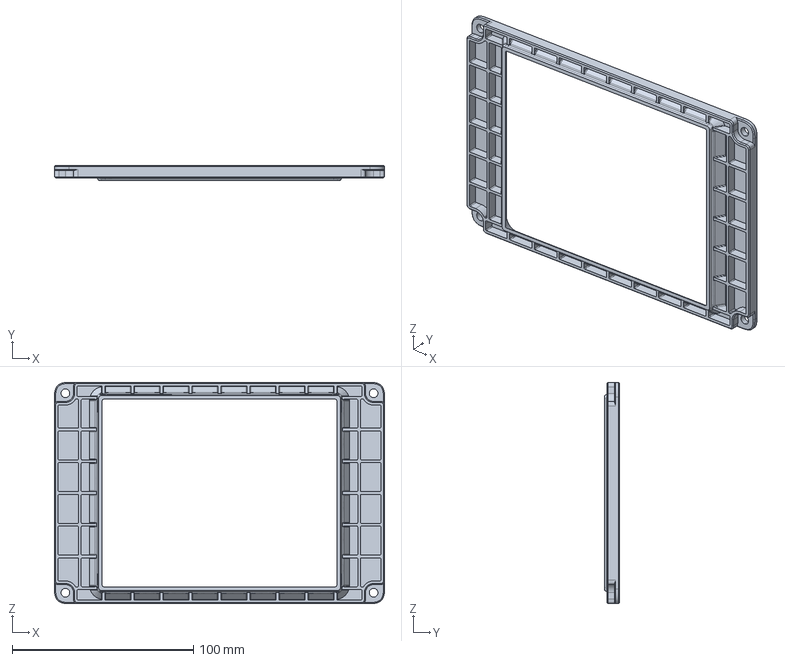
[picture p130: CAD file, 2026-01-14]
3d/big scanlight v1/25d111 valoi 360 advancer compatibility plate.step
182.0 x 8.50 x 122.0 mm
