jackw01/scanlight/3d/big scanlight v1/25d108a film carrier compatibility plate.step

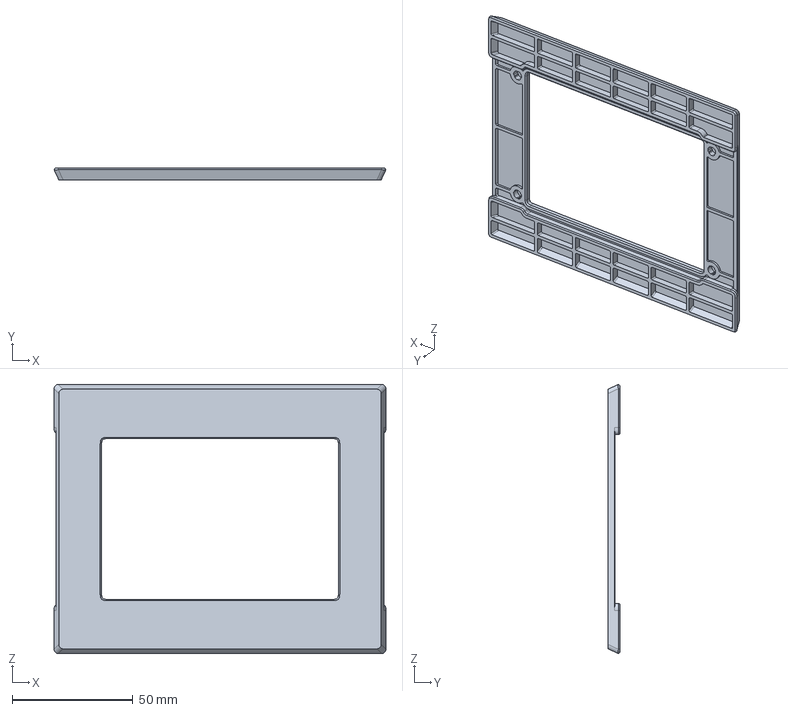
[picture p131: CAD file, 2025-12-28]
3d/big scanlight v1/25d108a film carrier compatibility plate.step
137.5 x 5.00 x 111.5 mm
